paguielng/noskipws/3dmodels/pan head cross recess screw_iso_ISO 7045 - M2 x 10 - Z - 10N.step

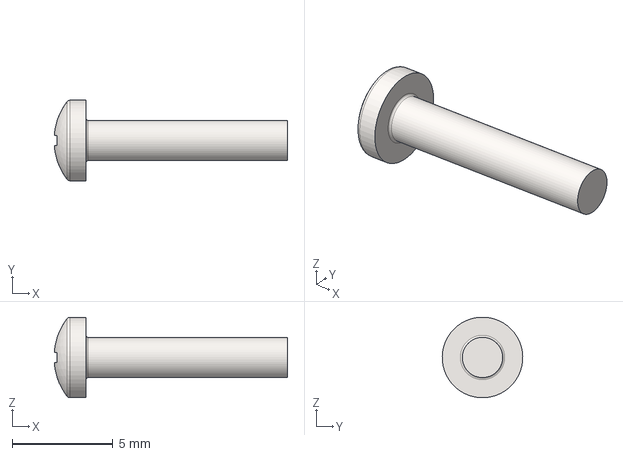
[picture p24: CAD file, 2025-12-07]
3dmodels/pan head cross recess screw_iso_ISO 7045 - M2 x 10 - Z - 10N.step
11.6 x 4.00 x 4.00 mm
