paguielng/noskipws/3dmodels/socket_button_head screw_iso_ISO 7380 - M3 x 6 - 6N/socket button head screw_iso_ISO 7380 - M3 x 6 - 6N.step

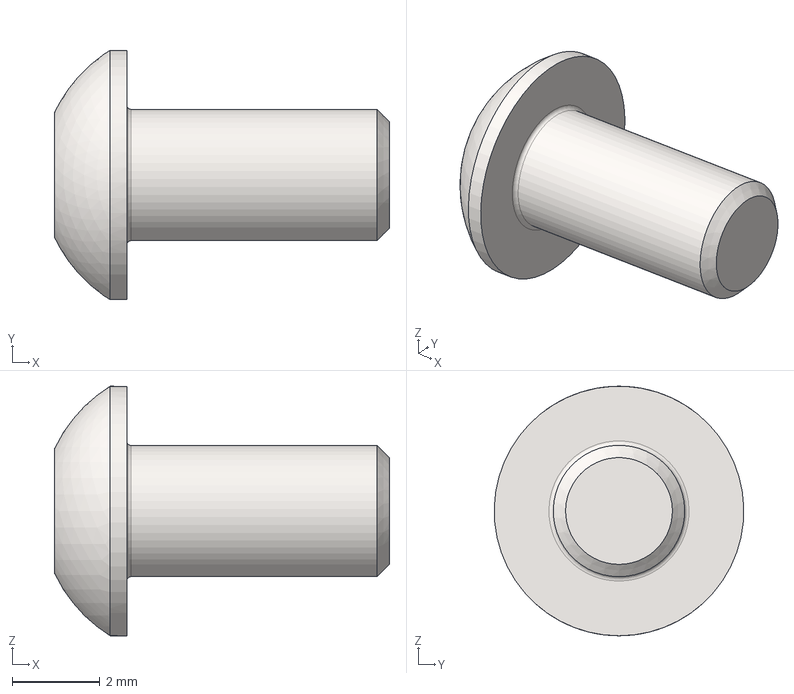
[picture p25: CAD file, 2025-12-04]
3dmodels/socket_button_head screw_iso_ISO 7380 - M3 x 6 - 6N/socket button head screw_iso_ISO 7380 - M3 x 6 - 6N.step
7.65 x 5.70 x 5.70 mm
