paguielng/noskipws/3dmodels/hex nut style 1 gradeab_iso_ISO - 4032 - M2 - W - N.step

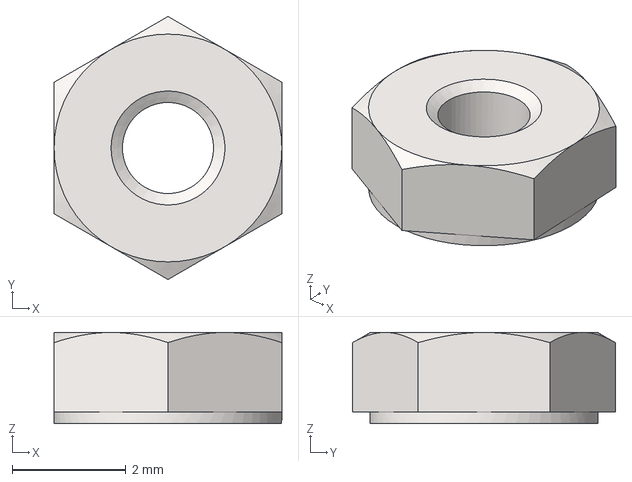
[picture p26: CAD file, 2025-12-07]
3dmodels/hex nut style 1 gradeab_iso_ISO - 4032 - M2 - W - N.step
4.00 x 4.62 x 1.60 mm
